EAHillebrand/smart-cpr-algo/src/New Folder/stm32f4discovery_gettingstarted_ert_rtw/rtmodel.h

/*
 * Academic License - for use in teaching, academic research, and meeting
 * course requirements at degree granting institutions only.  Not for
 * government, commercial, or other organizational use.
 *
 * File: rtmodel.h
 *
 * Code generated for Simulink model 'stm32f4discovery_gettingstarted'.
 *
 * Model version                  : 10.2
 * Simulink Coder version         : 9.6 (R2021b) 14-May-2021
 * C/C++ source code generated on : Fri Mar  3 15:09:37 2023
 *
 * Target selection: ert.tlc
 * Embedded hardware selection: ARM Compatible->ARM Cortex
 * Code generation objectives: Unspecified
 * Validation result: Not run
 */

#ifndef RTW_HEADER_rtmodel_h_
#define RTW_HEADER_rtmodel_h_
#include "stm32f4discovery_gettingstarted.h"

/* Macros generated for backwards compatibility  */
#ifndef rtmGetStopRequested
#define rtmGetStopRequested(rtm)       ((void*) 0)
#endif
#endif                                 /* RTW_HEADER_rtmodel_h_ */

/*
 * File trailer for generated code.
 *
 * [EOF]
 */
