EAHillebrand/smart-cpr-algo/src/New Folder/test1_forNano_ert_rtw/MW_target_hardware_resources.h

#ifndef PORTABLE_WORDSIZES
#ifdef __MW_TARGET_USE_HARDWARE_RESOURCES_H__
#ifndef __MW_TARGET_HARDWARE_RESOURCES_H__
#define __MW_TARGET_HARDWARE_RESOURCES_H__

#define MW_MULTI_TASKING_MODE 0
#include "nrf52840.h"
#include "MW_ArduinoHWInit.h"
#include "arduinoARMM4mbedScheduler.h"
#include "arm_cortex_m_multitasking.h"

#define MW_USECODERTARGET 1
#define MW_TARGETHARDWARE Arduino Nano 33 BLE Sense
#define MW_EXTMODEPROTOCOLINFO_XCPONSERIAL_HOSTINTERFACE Simulink
#define MW_EXTMODEPROTOCOLINFO_XCPONSERIAL_LOGGINGBUFFERAUTO 1
#define MW_EXTMODEPROTOCOLINFO_XCPONSERIAL_LOGGINGBUFFERSIZE 1000
#define MW_EXTMODEPROTOCOLINFO_XCPONSERIAL_LOGGINGBUFFERNUM 3
#define MW_CONNECTIONINFO_XCPONSERIAL_BAUDRATE codertarget.arduinobase.registry.getBaudRate
#define MW_CONNECTIONINFO_XCPONSERIAL_COMPORT codertarget.arduinobase.internal.getExternalModeMexArgs('Serial')
#define MW_CONNECTIONINFO_XCPONSERIAL_VERBOSE 0
#define MW_EXTMODE_CONFIGURATION XCP on Serial
#define MW_EXTMODE_COMPORTBAUD 921600
#define MW_RTOS Baremetal
#define MW_SCHEDULER_INTERRUPT_SOURCE 0
#define MW_RUNTIME_BUILDACTION 1
#define MW_RUNTIME_DISABLEPARALLELBUILD 0
#define MW_RUNTIME_FORCEBUILDSTATICLIBRARY 0
#define MW_HOSTCOMPORT_SET_HOST_COM_PORT 1
#define MW_HOSTCOMPORT_COM_PORT_NUMBER 4
#define MW_HOSTCOMPORT_BOOTLOADER_COM_PORT 2
#define MW_OVERRUNDETECTION_ENABLE_OVERRUN_DETECTION 0
#define MW_OVERRUNDETECTION_DIGITAL_OUTPUT_TO_SET_ON_OVERRUN 6
#define MW_ANALOGINREFVOLTAGE_ANALOG_INPUT_REFERENCE_VOLTAGE 0.000000
#define MW_SERIAL_SERIAL0_BAUD_RATE 3
#define MW_SERIAL_SERIAL1_BAUD_RATE 3
#define MW_I2C_I2C0BUSSPEEDHZ 100000
#define MW_SPI_SPI_CLOCK_OUT_FREQUENCY 2
#define MW_SPI_SPI_MODE 0
#define MW_SPI_SPI_BITORDER 0
#define MW_SPI_SDSLAVESELECT 4.000000
#define MW_SPI_CANCHIPSELECT 3.000000
#define MW_CAN_CANBUSSPEED 10
#define MW_CAN_CANOSCILLATORFREQUENCY 1
#define MW_CAN_INTERRUPTPIN 2.000000
#define MW_CAN_ALLOWALLFILTER 0
#define MW_CAN_BUFFER0IDTYPE 0
#define MW_CAN_ACCEPTANCEMASK0_NOR 0
#define MW_CAN_ACCEPTANCEFILTER0_NOR 255
#define MW_CAN_ACCEPTANCEFILTER1_NOR 255
#define MW_CAN_ACCEPTANCEMASK0_EXT 0
#define MW_CAN_ACCEPTANCEFILTER0_EXT 255
#define MW_CAN_ACCEPTANCEFILTER1_EXT 255
#define MW_CAN_BUFFER1IDTYPE 0
#define MW_CAN_ACCEPTANCEMASK1_NOR 0
#define MW_CAN_ACCEPTANCEFILTER2_NOR 255
#define MW_CAN_ACCEPTANCEFILTER3_NOR 255
#define MW_CAN_ACCEPTANCEFILTER4_NOR 255
#define MW_CAN_ACCEPTANCEFILTER5_NOR 255
#define MW_CAN_ACCEPTANCEMASK1_EXT 0
#define MW_CAN_ACCEPTANCEFILTER2_EXT 255
#define MW_CAN_ACCEPTANCEFILTER3_EXT 255
#define MW_CAN_ACCEPTANCEFILTER4_EXT 255
#define MW_CAN_ACCEPTANCEFILTER5_EXT 255
#define MW_DISPLAY_ENABLECODEGEN 0
#define MW_DISPLAY_APPLAUNCHBUTTON 
#define MW_BLE_PERIPHERAL_DEVICE_NAME Arduino
#define MW_BLE_PERIPHERAL_LOCAL_NAME Arduino
#define MW_BLE_ADVERTISING_INTERVAL 160
#define MW_BLE_MIN_CONNECTION_INTERVAL 6
#define MW_BLE_MAX_CONNECTION_INTERVAL 3200
#define MW_DATAVERSION 2016.02
#define MW_DASHBOARDCODEGENINFO_ENABLECODEGEN 0
#define MW_DASHBOARDCODEGENINFO_CIRCULARGAUGE_CODEGEN 1
#define MW_DASHBOARDCODEGENINFO_CIRCULARGAUGE_BLOCKCLASS codertarget.targetHiddenBlkInsert.internal.circularGauge
#define MW_DASHBOARDCODEGENINFO_CIRCULARGAUGE_REGFCN codertarget.arduinobase.blocks.registerDashboardBlk
#define MW_DASHBOARDCODEGENINFO_CIRCULARGAUGE_VALIDATEFCN codertarget.targetHiddenBlkInsert.internal.isDashboardBlockCodegenEnabled
#define MW_DASHBOARDCODEGENINFO_DISPLAYBLOCK_CODEGEN 1
#define MW_DASHBOARDCODEGENINFO_DISPLAYBLOCK_BLOCKCLASS codertarget.targetHiddenBlkInsert.internal.lcdTextDisplay
#define MW_DASHBOARDCODEGENINFO_DISPLAYBLOCK_REGFCN codertarget.arduinobase.blocks.registerDashboardBlk
#define MW_DASHBOARDCODEGENINFO_DISPLAYBLOCK_VALIDATEFCN codertarget.targetHiddenBlkInsert.internal.isDashboardBlockCodegenEnabled
#define MW_DASHBOARDCODEGENINFO_PUSHBUTTON_CODEGEN 1
#define MW_DASHBOARDCODEGENINFO_PUSHBUTTON_BLOCKCLASS codertarget.targetHiddenBlkInsert.internal.pushButton
#define MW_DASHBOARDCODEGENINFO_PUSHBUTTON_REGFCN codertarget.arduinobase.blocks.registerDashboardBlk
#define MW_DASHBOARDCODEGENINFO_PUSHBUTTON_VALIDATEFCN codertarget.targetHiddenBlkInsert.internal.isDashboardBlockCodegenEnabled

#endif /* __MW_TARGET_HARDWARE_RESOURCES_H__ */

#endif

#endif
