EAHillebrand/smart-cpr-algo/src/cpr-algo/test_ert_rtw/test.h

/*
 * test.h
 *
 * Academic License - for use in teaching, academic research, and meeting
 * course requirements at degree granting institutions only.  Not for
 * government, commercial, or other organizational use.
 *
 * Code generation for model "test".
 *
 * Model version              : 1.1
 * Simulink Coder version : 9.6 (R2021b) 14-May-2021
 * C source code generated on : Tue Feb  7 12:17:20 2023
 *
 * Target selection: ert.tlc
 * Embedded hardware selection: ARM Compatible->ARM Cortex
 * Code generation objectives: Unspecified
 * Validation result: Not run
 */

#ifndef RTW_HEADER_test_h_
#define RTW_HEADER_test_h_
#include <math.h>
#include <stddef.h>
#include <string.h>
#ifndef test_COMMON_INCLUDES_
#define test_COMMON_INCLUDES_
#include "rtwtypes.h"
#include "rtw_continuous.h"
#include "rtw_solver.h"
#include "main.h"
#endif                                 /* test_COMMON_INCLUDES_ */

#include "test_types.h"
#include "MW_target_hardware_resources.h"

/* Macros for accessing real-time model data structure */
#ifndef rtmGetErrorStatus
#define rtmGetErrorStatus(rtm)         ((rtm)->errorStatus)
#endif

#ifndef rtmSetErrorStatus
#define rtmSetErrorStatus(rtm, val)    ((rtm)->errorStatus = (val))
#endif

/* Block states (default storage) for system '<Root>' */
typedef struct {
  int32_T counter;                     /* '<Root>/Sine Wave' */
} DW_test_T;

/* Parameters (default storage) */
struct P_test_T_ {
  real_T CompareToConstant_const;     /* Mask Parameter: CompareToConstant_const
                                       * Referenced by: '<S1>/Constant'
                                       */
  real_T ON_Value;                     /* Expression: 1
                                        * Referenced by: '<Root>/ON'
                                        */
  real_T OFF_Value;                    /* Expression: 0
                                        * Referenced by: '<Root>/OFF'
                                        */
  real_T SineWave_Amp;                 /* Expression: 5
                                        * Referenced by: '<Root>/Sine Wave'
                                        */
  real_T SineWave_Bias;                /* Expression: 0
                                        * Referenced by: '<Root>/Sine Wave'
                                        */
  real_T SineWave_NumSamp;             /* Expression: 10
                                        * Referenced by: '<Root>/Sine Wave'
                                        */
  real_T SineWave_Offset;              /* Expression: 0
                                        * Referenced by: '<Root>/Sine Wave'
                                        */
};

/* Real-time Model Data Structure */
struct tag_RTM_test_T {
  const char_T * volatile errorStatus;
};

/* Block parameters (default storage) */
extern P_test_T test_P;

/* Block states (default storage) */
extern DW_test_T test_DW;

/* Model entry point functions */
extern void test_initialize(void);
extern void test_step(void);
extern void test_terminate(void);

/* Real-time Model object */
extern RT_MODEL_test_T *const test_M;
extern volatile boolean_T stopRequested;
extern volatile boolean_T runModel;

/*-
 * These blocks were eliminated from the model due to optimizations:
 *
 * Block '<Root>/Scope' : Unused code path elimination
 */

/*-
 * The generated code includes comments that allow you to trace directly
 * back to the appropriate location in the model.  The basic format
 * is <system>/block_name, where system is the system number (uniquely
 * assigned by Simulink) and block_name is the name of the block.
 *
 * Use the MATLAB hilite_system command to trace the generated code back
 * to the model.  For example,
 *
 * hilite_system('<S3>')    - opens system 3
 * hilite_system('<S3>/Kp') - opens and selects block Kp which resides in S3
 *
 * Here is the system hierarchy for this model
 *
 * '<Root>' : 'test'
 * '<S1>'   : 'test/Compare To Constant'
 * '<S2>'   : 'test/Digital Port Write'
 * '<S3>'   : 'test/Digital Port Write/ECSoC'
 * '<S4>'   : 'test/Digital Port Write/ECSoC/ECSimCodegen'
 */
#endif                                 /* RTW_HEADER_test_h_ */
